SunritHazra/HackroPadX/Media/HackroPadX Fusion Teams Render.jpg

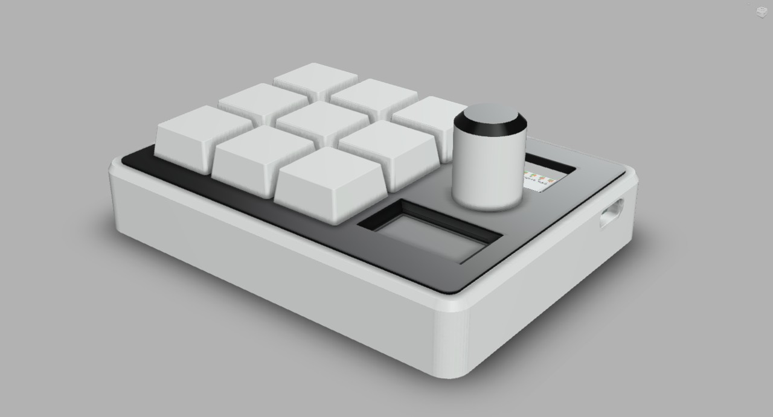
Media/HackroPadX Fusion Teams Render.jpg
